phoezelle/player-entre-chien-et-loup/Player/doc/html/class_sd_fat_soft_spi.png

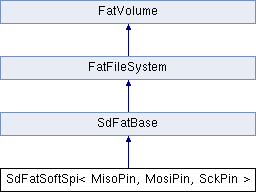
Player/doc/html/class_sd_fat_soft_spi.png
