phoezelle/player-entre-chien-et-loup/Player/doc/html/class_sd_file.png

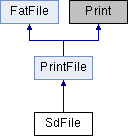
Player/doc/html/class_sd_file.png
