phoezelle/player-entre-chien-et-loup/Player/doc/html/classios.png

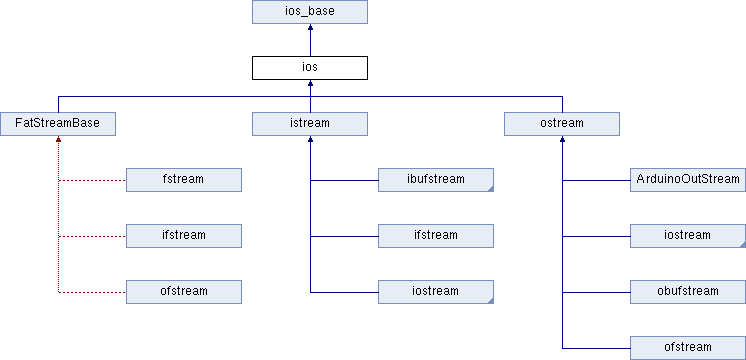
Player/doc/html/classios.png
