phoezelle/player-entre-chien-et-loup/Remote/PlayerAndRemotecommons.h

//
//  PlayerAndRemotecommons.h
//  
//
//  Created by Pierre Hoezelle on 14/11/12.
//  Copyright (c) 2012 __MyCompanyName__. All rights reserved.
//

#ifndef _PlayerAndRemotecommons_h
#define _PlayerAndRemotecommons_h



#endif
